aindustriosa/RustyBugA_Gateway/docs/images/5992470695482871092.jpg

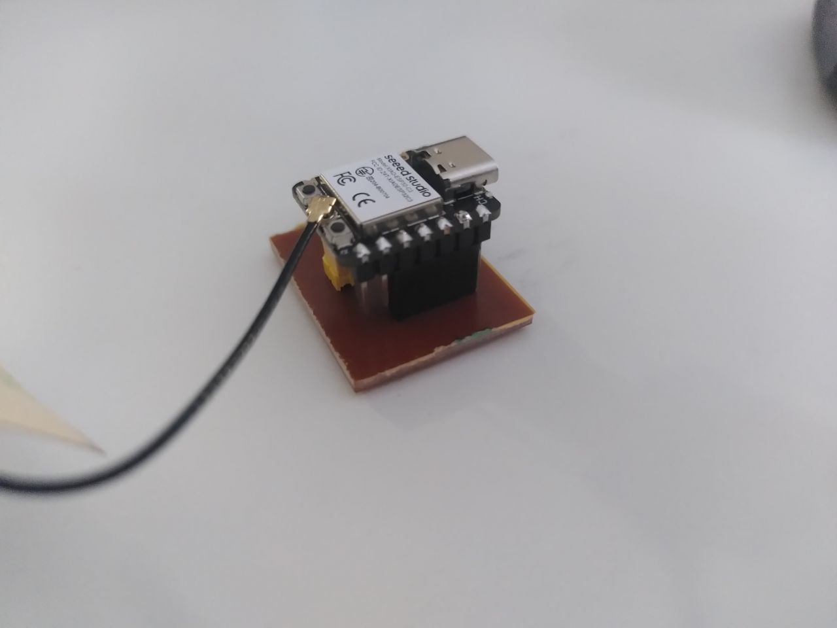
docs/images/5992470695482871092.jpg
