aindustriosa/RustyBugA_Gateway/src/secrets_example.hpp

char WIFI_SSID[] = "hello_ssid";
char WIFI_PASS[] = "a_password";

// mDNS hostname for the device
// This will be used to access the device via mDNS, e.g., nc -u mighty_logger_1.local 1234
char MDNS_HOSTNAME[] = "mighty_logger_1";

const unsigned int SERVER_PORT = 1234; // UDP server port
